sparkfun/SparkFun_GNSS_mosaic-T/docs/assets/3d_model/poster.png

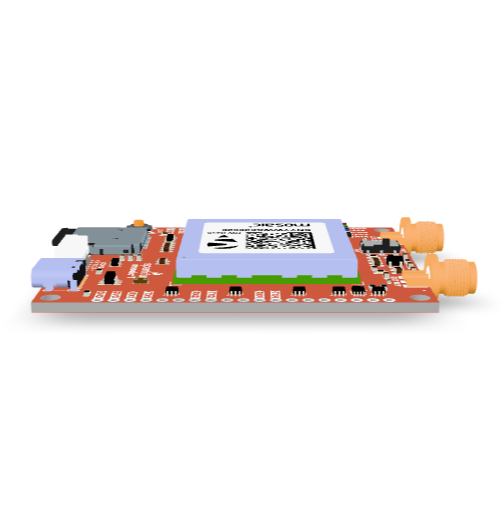
docs/assets/3d_model/poster.png
