sparkfun/SparkFun_GNSS_mosaic-T/docs/assets/img/hookup_guide/pi-network_configuration.gif

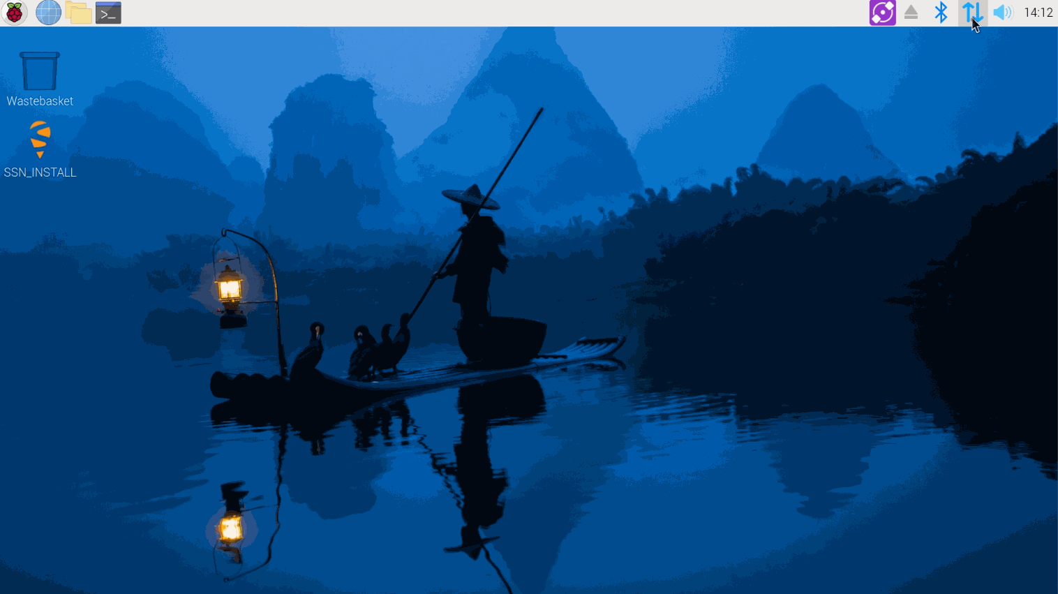
docs/assets/img/hookup_guide/pi-network_configuration.gif
