sparkfun/SparkFun_GNSS_mosaic-T/docs/assets/img/hookup_guide/pi-network_connections.png

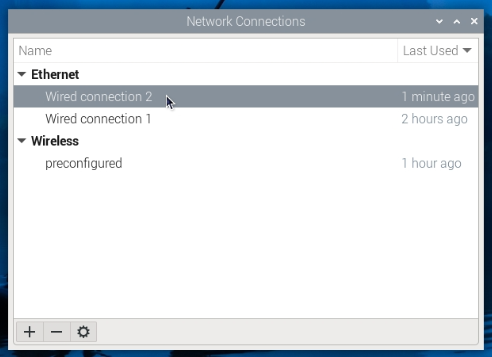
docs/assets/img/hookup_guide/pi-network_connections.png
